stefanofinetti/MF_OverHead_Panel/STL Files/FaceDown_Printing/OVHD_PANEL_APU_UPPER_LAYER_TRASP.stl

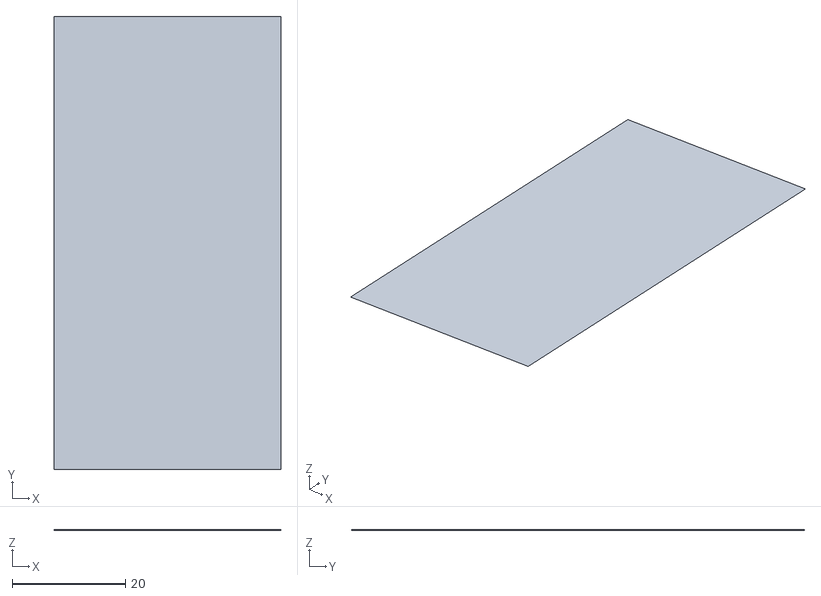
[picture p44: CAD file, 2025-06-21]
STL Files/FaceDown_Printing/OVHD_PANEL_APU_UPPER_LAYER_TRASP.stl
40.0 x 80.0 x 0.1
