stefanofinetti/MF_OverHead_Panel/STL Files/OVHD_OPEN_ON_KORRY_BUTTON_BLACK.stl

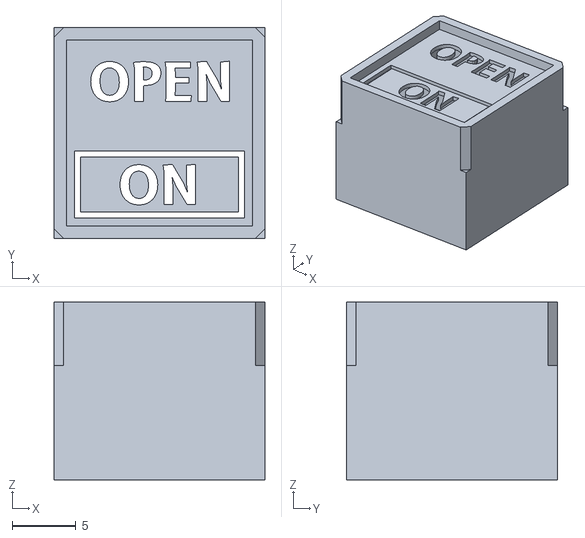
[picture p45: CAD file, 2025-01-15]
STL Files/OVHD_OPEN_ON_KORRY_BUTTON_BLACK.stl
16.6 x 16.6 x 14.0
