stefanofinetti/MF_OverHead_Panel/STL Files/FaceDown_Printing/OVHD_PANEL_APU_FRAME_TRASP.stl

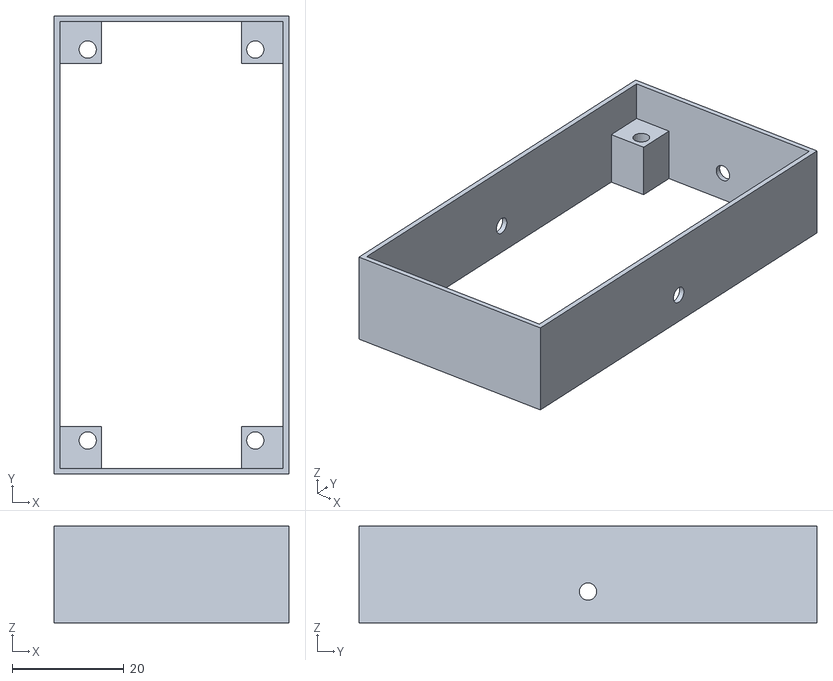
[picture p46: CAD file, 2025-06-21]
STL Files/FaceDown_Printing/OVHD_PANEL_APU_FRAME_TRASP.stl
42.0 x 82.0 x 17.3
