stefanofinetti/MF_OverHead_Panel/STL Files/Levers/obj_2_emer_lts.stl

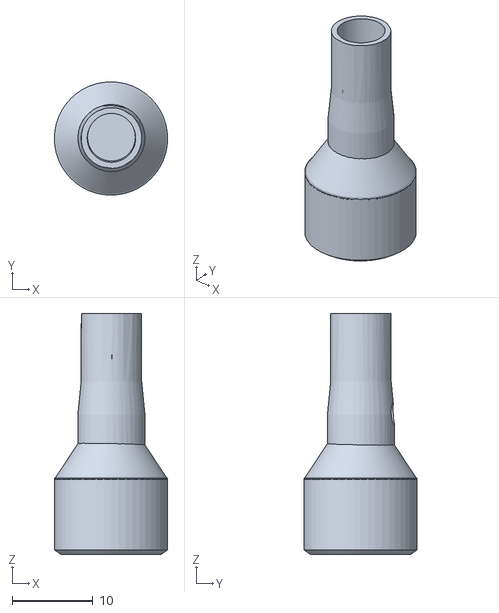
[picture p47: CAD file, 2026-09-29]
STL Files/Levers/obj_2_emer_lts.stl
14.0 x 14.0 x 29.8
