stefanofinetti/MF_OverHead_Panel/STL Files/Levers/Landing-Stem-Landing Lights Stem.stl

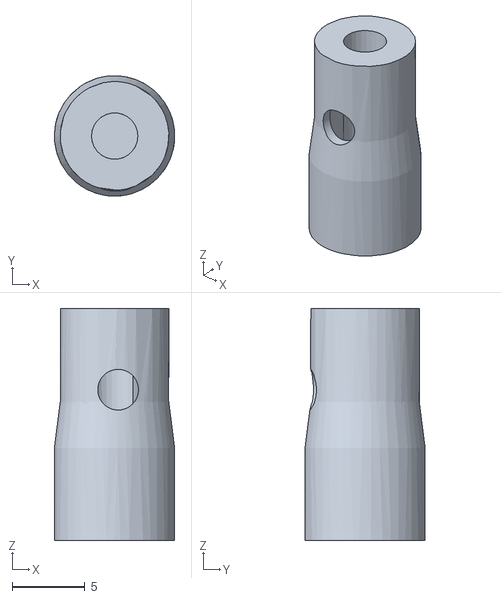
[picture p48: CAD file, 2026-09-29]
STL Files/Levers/Landing-Stem-Landing Lights Stem.stl
8.30 x 8.30 x 16.0
