stefanofinetti/MF_OverHead_Panel/STL Files/OVHD_FAULT_OFF_KORRY_BUTTON_TRANSP.stl

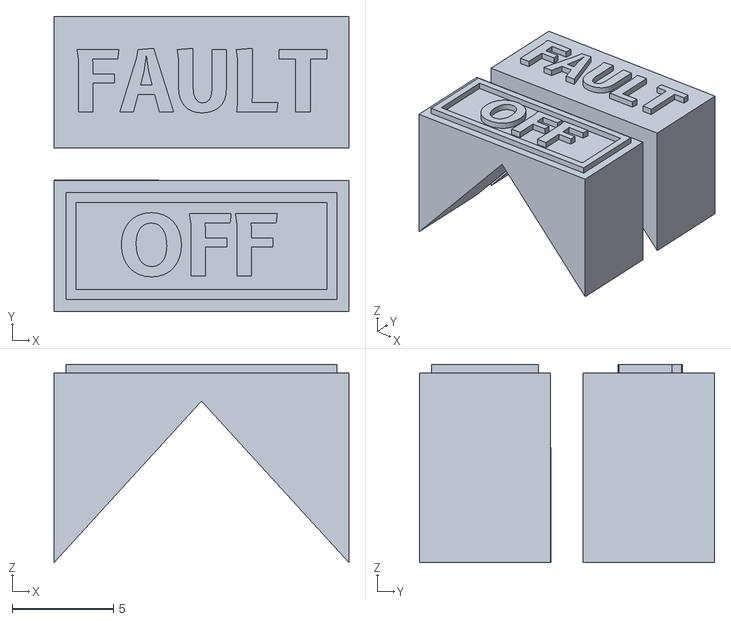
[picture p49: CAD file, 2025-01-15]
STL Files/OVHD_FAULT_OFF_KORRY_BUTTON_TRANSP.stl
14.6 x 14.6 x 9.82
