stefanofinetti/MF_OverHead_Panel/STL Files/Levers/landing-lights.stl

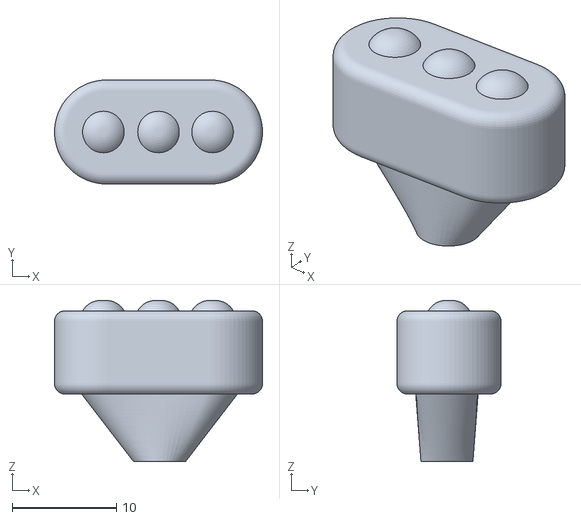
[picture p50: CAD file, 2025-01-14]
STL Files/Levers/landing-lights.stl
20.0 x 10.0 x 15.5
