stefanofinetti/MF_OverHead_Panel/STL Files/OVHD_KORRY_BUTTONS_SET.3mf

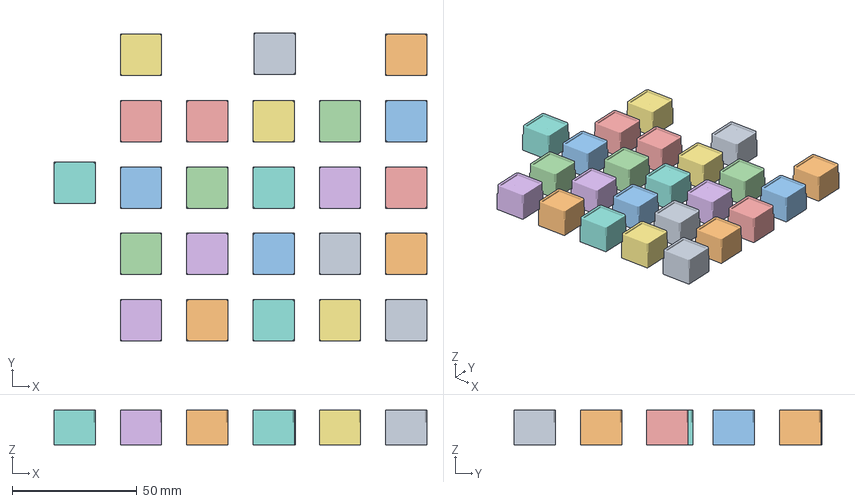
[picture p51: CAD file, 2025-01-15]
STL Files/OVHD_KORRY_BUTTONS_SET.3mf
149.6 x 123.5 x 14.0 mm
OVHD_AVAIL_ON_KORRY_BUTTON_BLACK x 2
OVHD_ON_KORRY_BUTTON_BLACK
OVHD_FAULT_ON_KORRY_BUTTON_BLACK x 5
OVHD_FAULT_OFF_KORRY_BUTTON_BLACK x 12
OVHD_OPEN_ON_KORRY_BUTTON_BLACK
OVHD_OFF_KORRY_BUTTON_BLACK x 3
