stefanofinetti/MF_OverHead_Panel/STL Files/OVHD_ON_KORRY_BUTTON_TRASP.stl

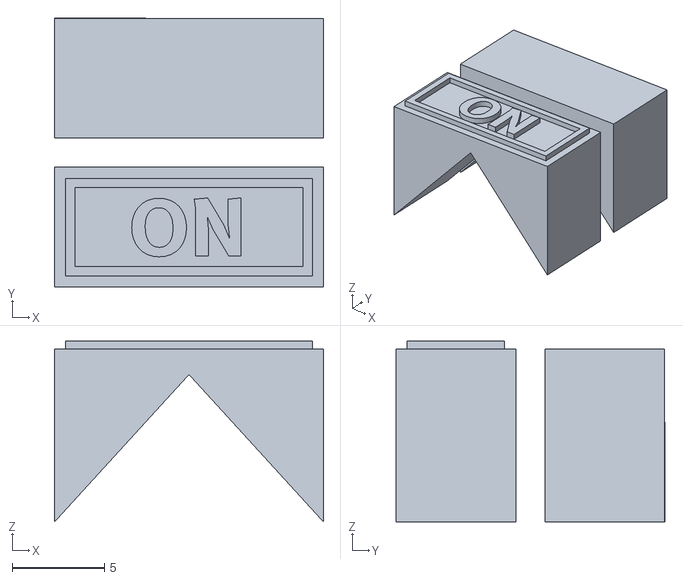
[picture p52: CAD file, 2025-01-15]
STL Files/OVHD_ON_KORRY_BUTTON_TRASP.stl
14.6 x 14.6 x 9.82
