stefanofinetti/MF_OverHead_Panel/STL Files/Levers/taxi-light.stl

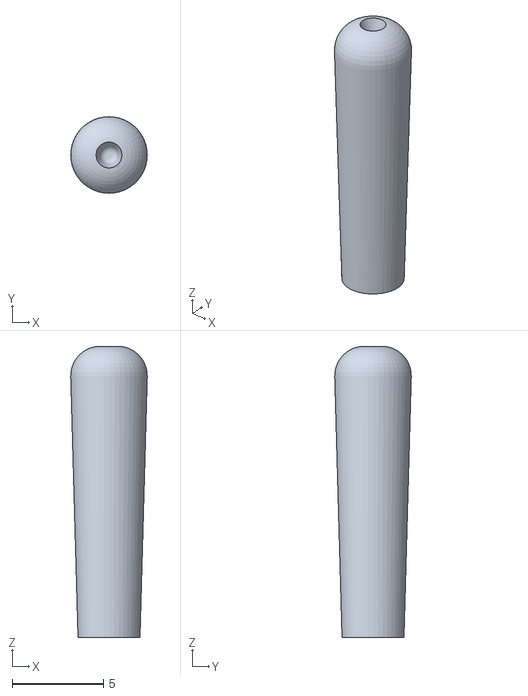
[picture p53: CAD file, 2025-01-14]
STL Files/Levers/taxi-light.stl
4.20 x 4.20 x 16.0
