stefanofinetti/MF_OverHead_Panel/STL Files/Levers/strobe-light.stl

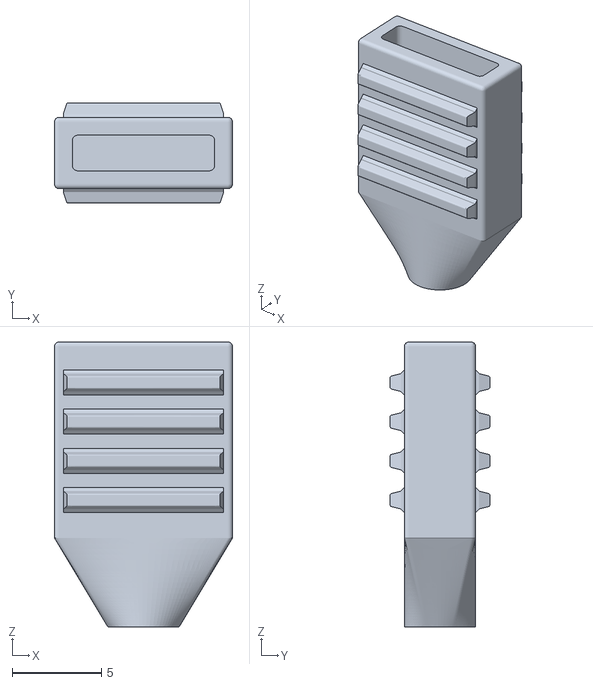
[picture p54: CAD file, 2025-01-14]
STL Files/Levers/strobe-light.stl
10.0 x 5.60 x 16.0
