stefanofinetti/MF_OverHead_Panel/STL Files/OVHD_PANEL_EXTLT.3mf

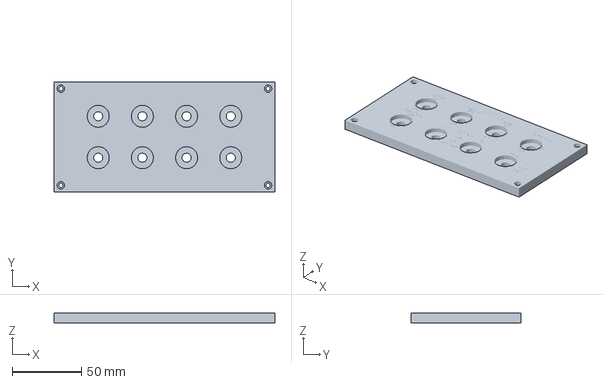
[picture p56: CAD file, 2025-01-14]
STL Files/OVHD_PANEL_EXTLT.3mf
160.0 x 80.0 x 7.56 mm
