stefanofinetti/MF_OverHead_Panel/STL Files/OVHD_PANEL_SIGNS_BLACK.stl

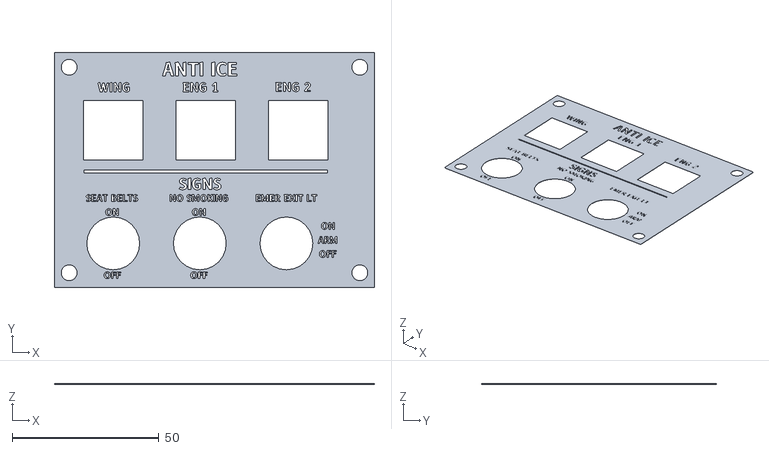
[picture p57: CAD file, 2025-01-14]
STL Files/OVHD_PANEL_SIGNS_BLACK.stl
109.0 x 80.0 x 0.42
