stefanofinetti/MF_OverHead_Panel/STL Files/OVHD_PANEL_SIGNS.3mf

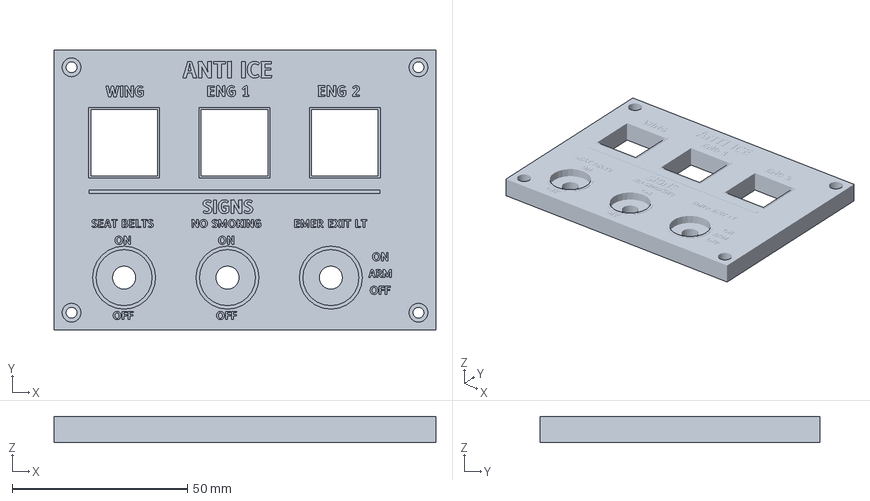
[picture p58: CAD file, 2025-01-14]
STL Files/OVHD_PANEL_SIGNS.3mf
109.0 x 80.0 x 7.56 mm
