stefanofinetti/MF_OverHead_Panel/STL Files/OVHD_PANEL_EXTLT_GRAY.stl

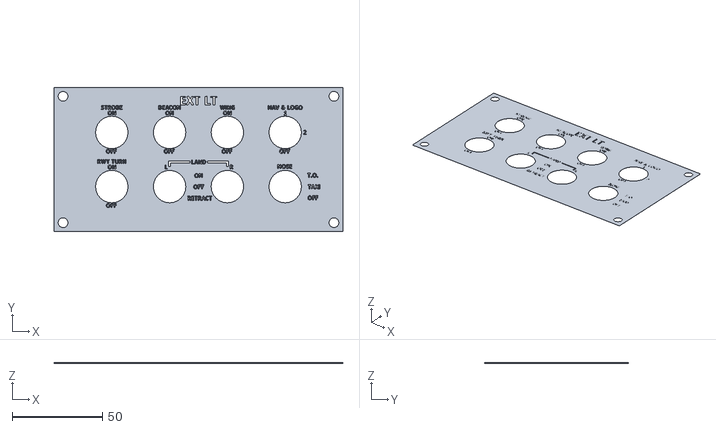
[picture p59: CAD file, 2025-01-14]
STL Files/OVHD_PANEL_EXTLT_GRAY.stl
160.0 x 80.0 x 0.42
