stefanofinetti/MF_OverHead_Panel/STL Files/OVHD_PANEL_SIGNS_TRASP.stl

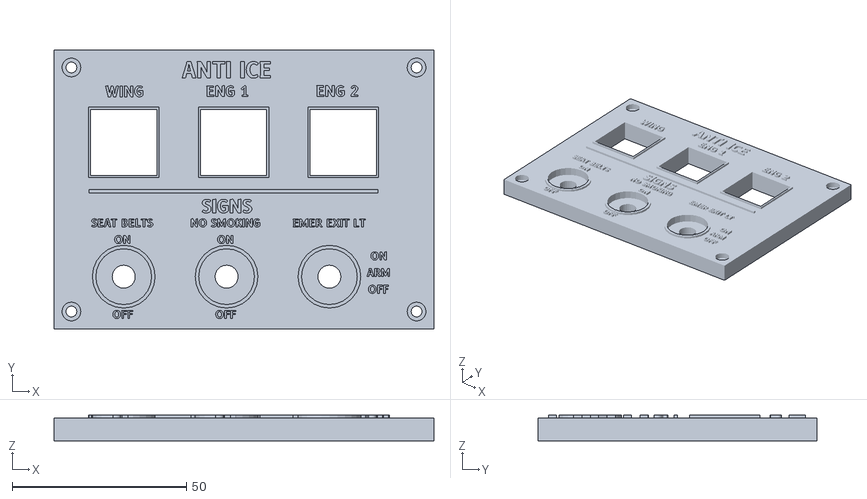
[picture p61: CAD file, 2025-01-14]
STL Files/OVHD_PANEL_SIGNS_TRASP.stl
109.0 x 80.0 x 7.42
