stefanofinetti/MF_OverHead_Panel/STL Files/OVHD_Switching_Knobs .3mf

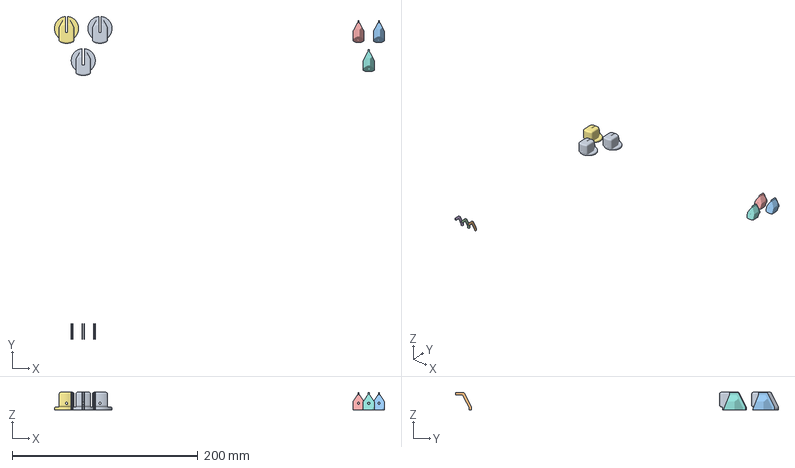
[picture p62: CAD file, 2025-01-14]
STL Files/OVHD_Switching_Knobs .3mf
355.2 x 347.6 x 19.0 mm
ecam-switching-knobs-ma22-knob-body.stl x 3
ecam-switching-knobs-ma22-black-line-surrounds.stl x 3
ecam-switching-knobs-ma22-light-pipe-body.stl x 3
