stefanofinetti/MF_OverHead_Panel/STL Files/OVHD_PANEL_EXTLT_TRASP.stl

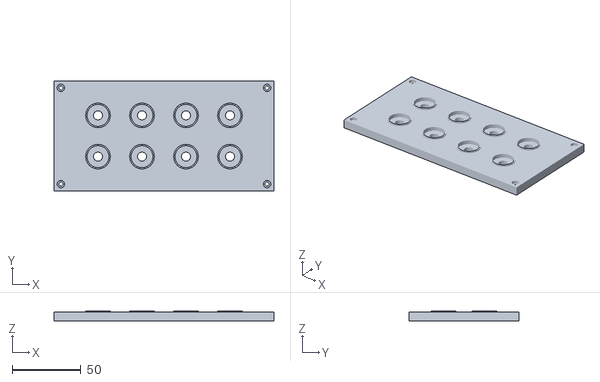
[picture p63: CAD file, 2025-01-14]
STL Files/OVHD_PANEL_EXTLT_TRASP.stl
160.0 x 80.0 x 7.42
