stefanofinetti/MF_OverHead_Panel/STL Files/OVHD_PANEL_LOWER_LEFT_CASE_BLACK.3mf

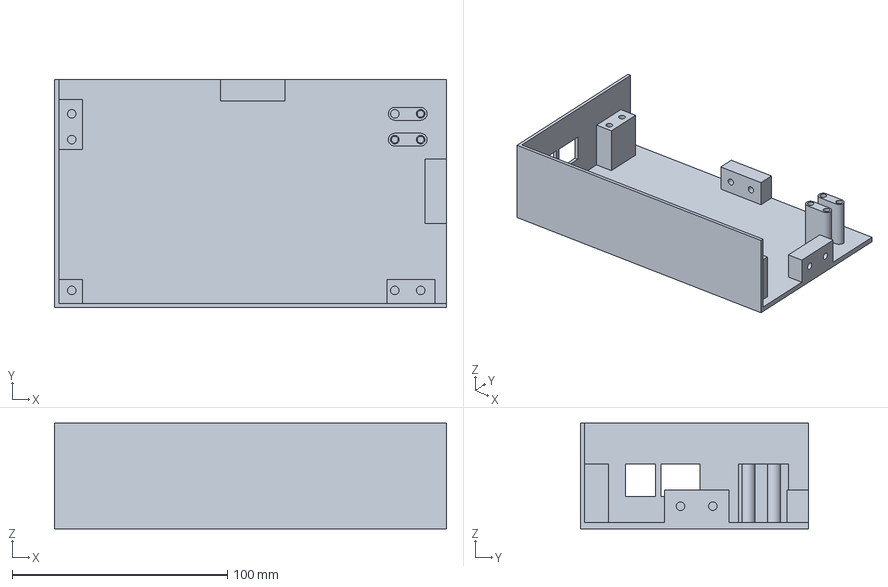
[picture p64: CAD file, 2025-01-14]
STL Files/OVHD_PANEL_LOWER_LEFT_CASE_BLACK.3mf
182.0 x 106.0 x 49.0 mm
