stefanofinetti/MF_OverHead_Panel/STL Files/OVHD_PANEL_UPPER_RIGHT_CASE_BLACK.3mf

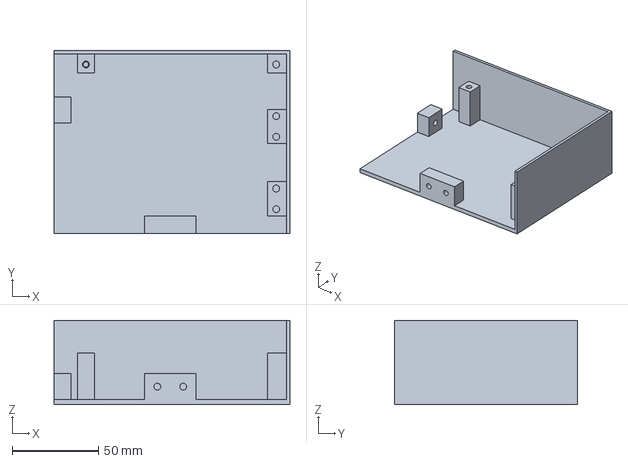
[picture p65: CAD file, 2025-01-14]
STL Files/OVHD_PANEL_UPPER_RIGHT_CASE_BLACK.3mf
137.0 x 106.0 x 49.0 mm
