stefanofinetti/MF_OverHead_Panel/STL Files/OVHD_PANEL_SIGNS_WHITE.stl

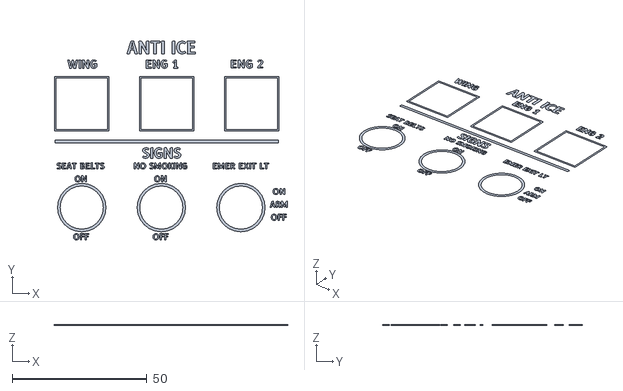
[picture p66: CAD file, 2025-01-14]
STL Files/OVHD_PANEL_SIGNS_WHITE.stl
86.4 x 73.8 x 0.14
