stefanofinetti/MF_OverHead_Panel/STL Files/OVHD_KORRY_CASE_SHORT_TRIPLE_19x19.stl

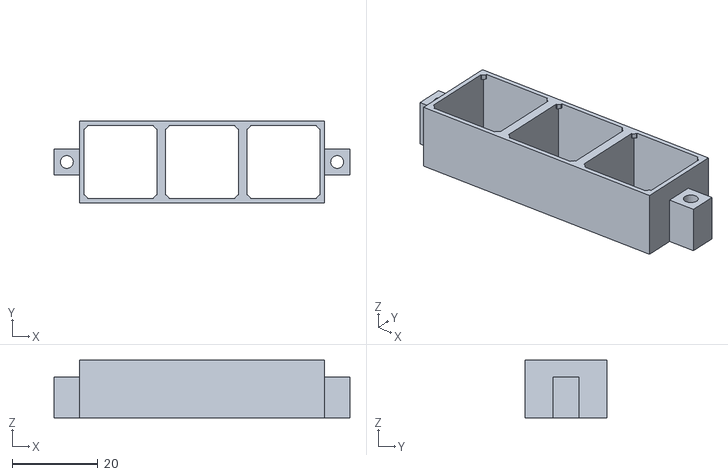
[picture p67: CAD file, 2024-12-02]
STL Files/OVHD_KORRY_CASE_SHORT_TRIPLE_19x19.stl
69.0 x 19.0 x 13.5
