stefanofinetti/MF_OverHead_Panel/STL Files/OVHD_PANEL_FUEL_TRASP.stl

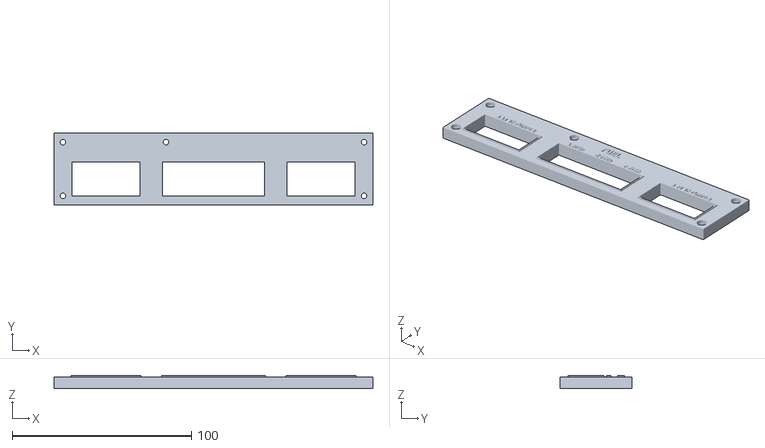
[picture p68: CAD file, 2024-12-02]
STL Files/OVHD_PANEL_FUEL_TRASP.stl
178.0 x 40.0 x 7.42
