stefanofinetti/MF_OverHead_Panel/STL Files/OVHD_PANEL_FUEL_GRAY.stl

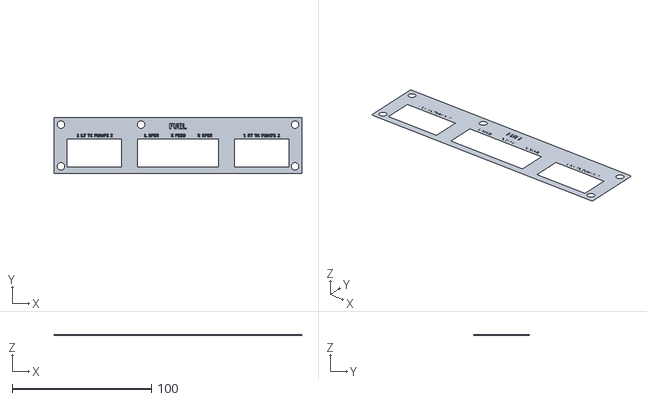
[picture p69: CAD file, 2024-12-02]
STL Files/OVHD_PANEL_FUEL_GRAY.stl
178.0 x 40.0 x 0.42
