stefanofinetti/MF_OverHead_Panel/STL Files/OVHD_PANEL_FUEL_WHITE.stl

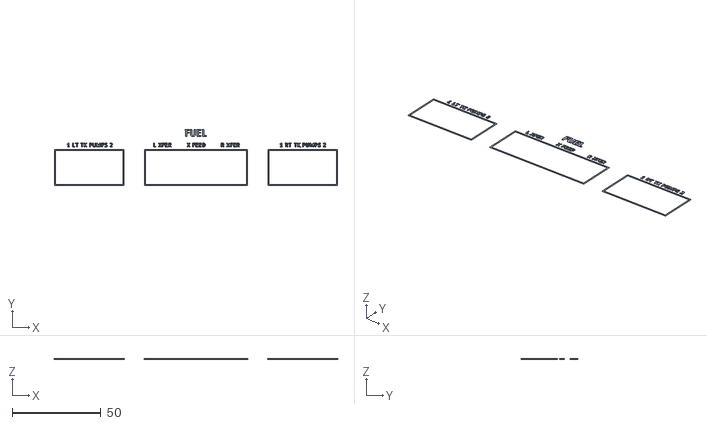
[picture p72: CAD file, 2024-12-02]
STL Files/OVHD_PANEL_FUEL_WHITE.stl
159.2 x 31.6 x 0.14
