stefanofinetti/MF_OverHead_Panel/STL Files/OVHD_PANEL_AIR-COND_FRAME_WHITE.stl

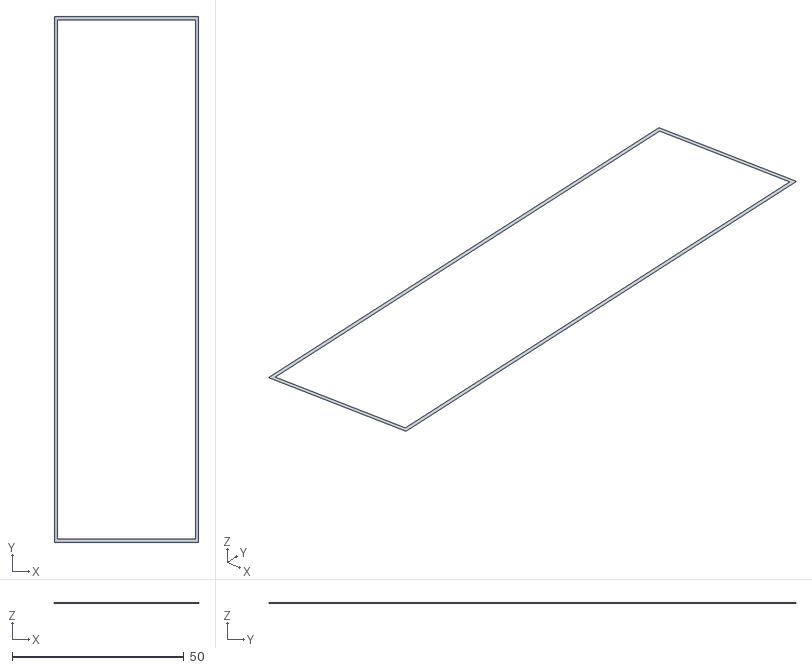
[picture p73: CAD file, 2024-12-02]
STL Files/OVHD_PANEL_AIR-COND_FRAME_WHITE.stl
42.0 x 153.0 x 0.14
