stefanofinetti/MF_OverHead_Panel/STL Files/OVHD_PANEL_AIRCOND_GRAY.stl

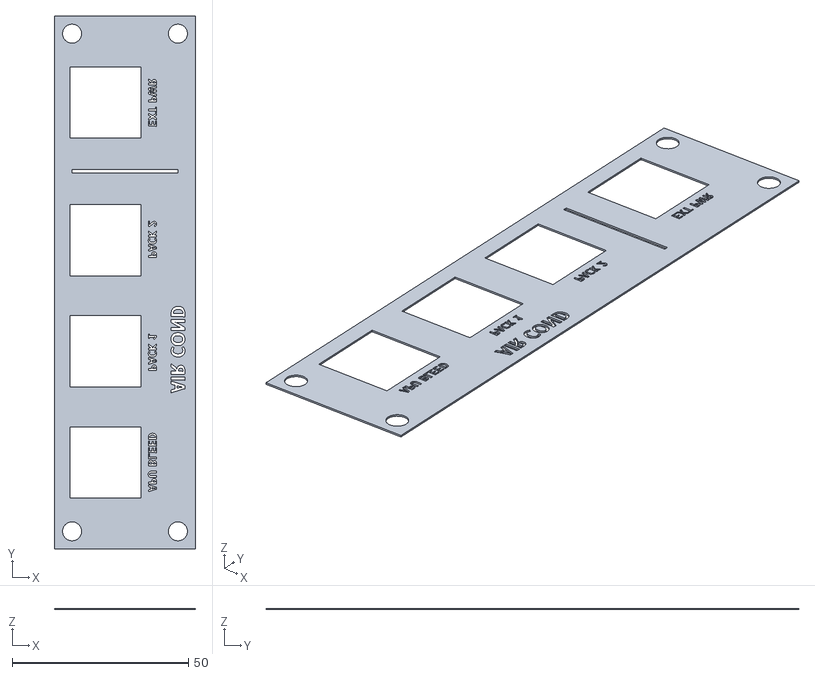
[picture p74: CAD file, 2024-12-02]
STL Files/OVHD_PANEL_AIRCOND_GRAY.stl
40.0 x 151.0 x 0.42
