stefanofinetti/MF_OverHead_Panel/STL Files/OVHD_PANEL_ELEC_FRAME_TRASP.stl

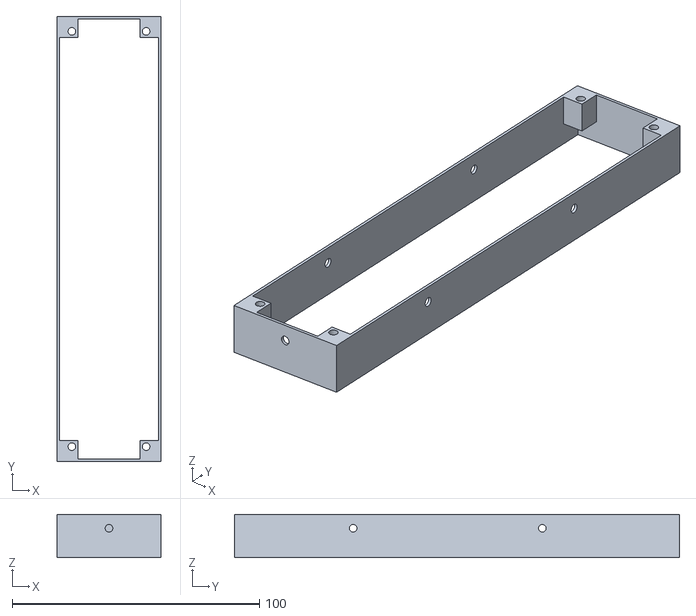
[picture p75: CAD file, 2024-12-02]
STL Files/OVHD_PANEL_ELEC_FRAME_TRASP.stl
42.0 x 180.0 x 17.4
