stefanofinetti/MF_OverHead_Panel/STL Files/OVHD_PANEL_GPWS_GRAY.stl

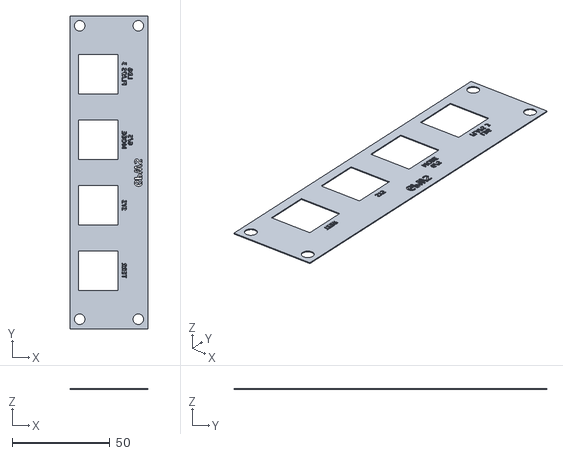
[picture p76: CAD file, 2024-12-02]
STL Files/OVHD_PANEL_GPWS_GRAY.stl
40.0 x 160.0 x 0.42
