stefanofinetti/MF_OverHead_Panel/STL Files/OVHD_PANEL_AIRCOND_WHITE.stl

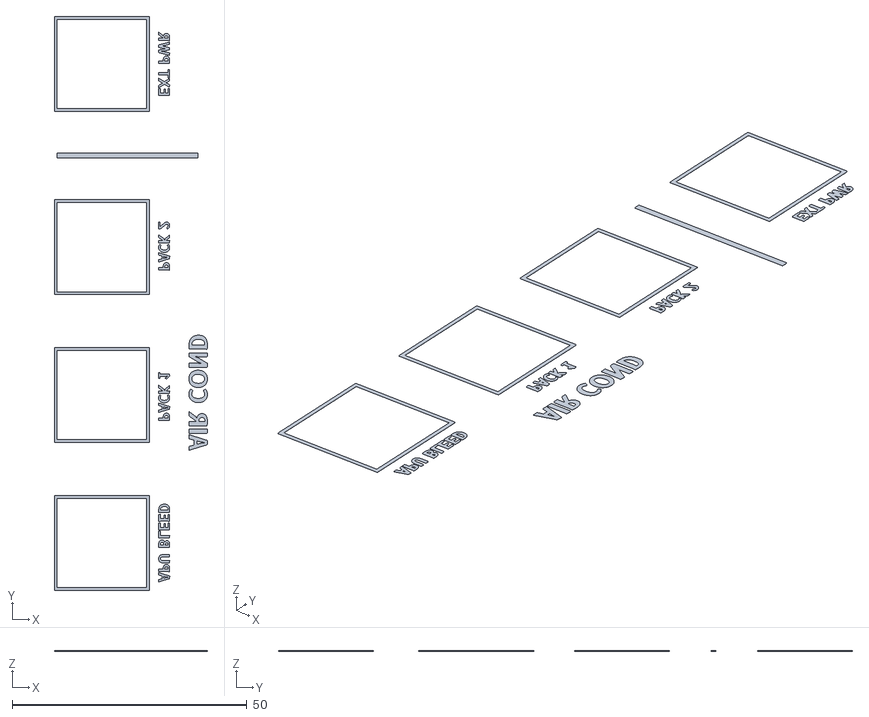
[picture p77: CAD file, 2024-12-02]
STL Files/OVHD_PANEL_AIRCOND_WHITE.stl
32.6 x 122.2 x 0.14
