stefanofinetti/MF_OverHead_Panel/STL Files/OVHD_PANEL_APU_CONCEPT_BLACK.stl

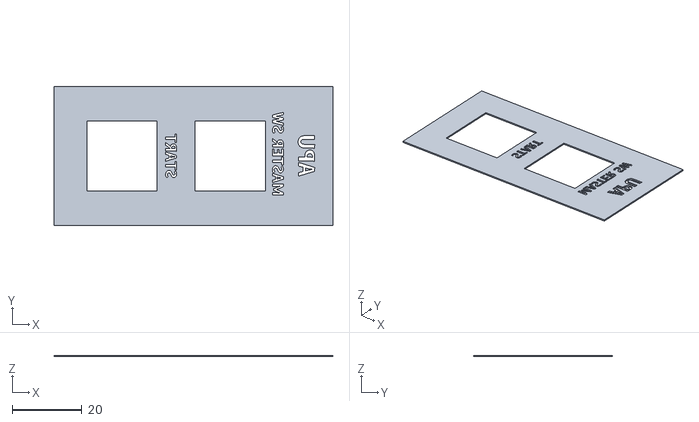
[picture p78: CAD file, 2024-12-02]
STL Files/OVHD_PANEL_APU_CONCEPT_BLACK.stl
80.0 x 40.0 x 0.42
