stefanofinetti/MF_OverHead_Panel/STL Files/OVHD_PANEL_ELEC_GRAY.stl

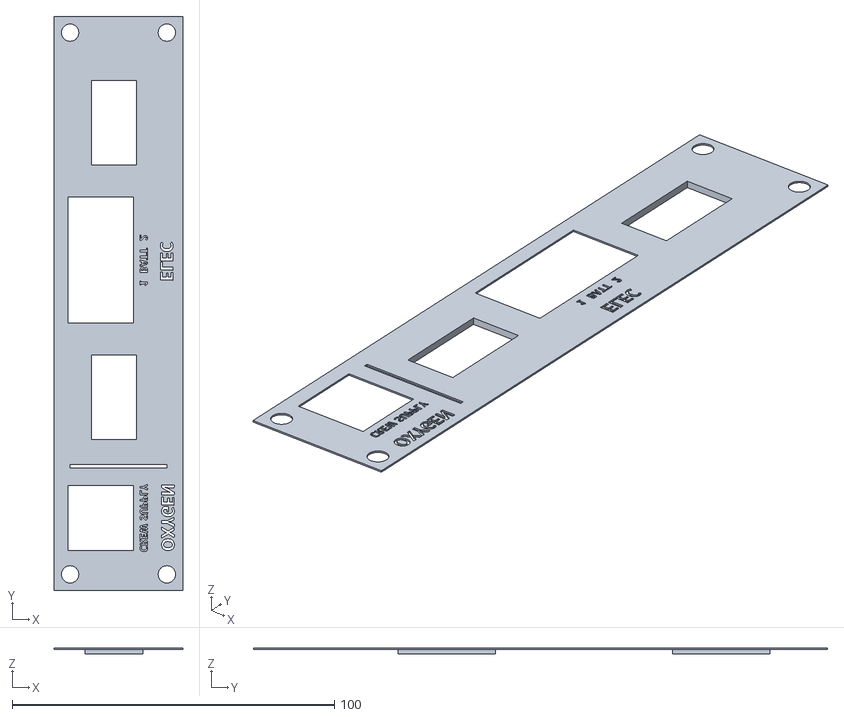
[picture p79: CAD file, 2024-12-02]
STL Files/OVHD_PANEL_ELEC_GRAY.stl
40.0 x 178.0 x 1.82
