stefanofinetti/MF_OverHead_Panel/STL Files/OVHD_KORRY_CASE_SHORT_19x19.stl

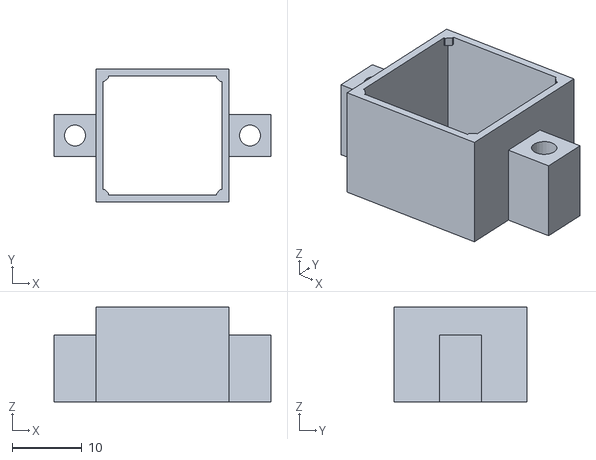
[picture p81: CAD file, 2024-12-02]
STL Files/OVHD_KORRY_CASE_SHORT_19x19.stl
31.0 x 19.0 x 13.5
