stefanofinetti/MF_OverHead_Panel/STL Files/OVHD_PANEL_ELEC_WHITE.stl

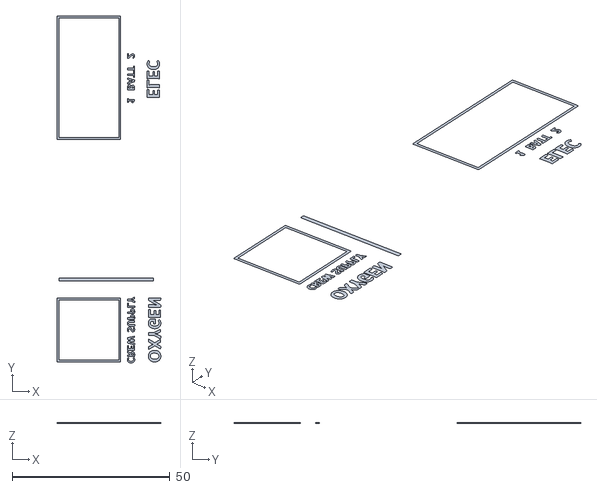
[picture p82: CAD file, 2024-12-02]
STL Files/OVHD_PANEL_ELEC_WHITE.stl
33.0 x 110.1 x 0.14
