stefanofinetti/MF_OverHead_Panel/STL Files/OVHD_PANEL_ELEC_FRAME_WHITE.stl

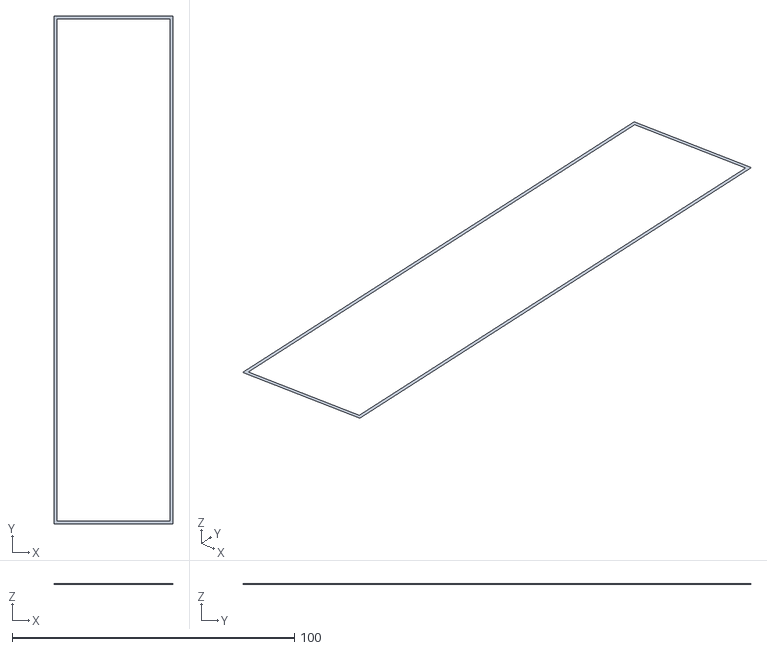
[picture p83: CAD file, 2024-12-02]
STL Files/OVHD_PANEL_ELEC_FRAME_WHITE.stl
42.0 x 180.0 x 0.14
