stefanofinetti/MF_OverHead_Panel/STL Files/OVHD_PANEL_APU_FRAME_TRASP.stl

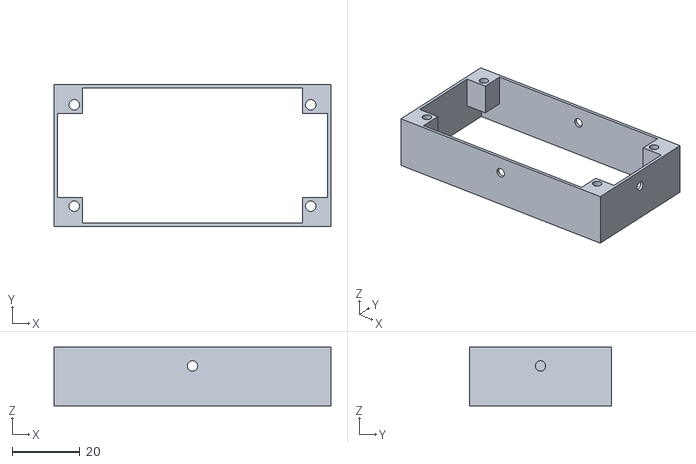
[picture p84: CAD file, 2024-12-02]
STL Files/OVHD_PANEL_APU_FRAME_TRASP.stl
82.0 x 42.0 x 17.4
