stefanofinetti/MF_OverHead_Panel/STL Files/OVHD_PANEL_EXTLT_WHITE.stl

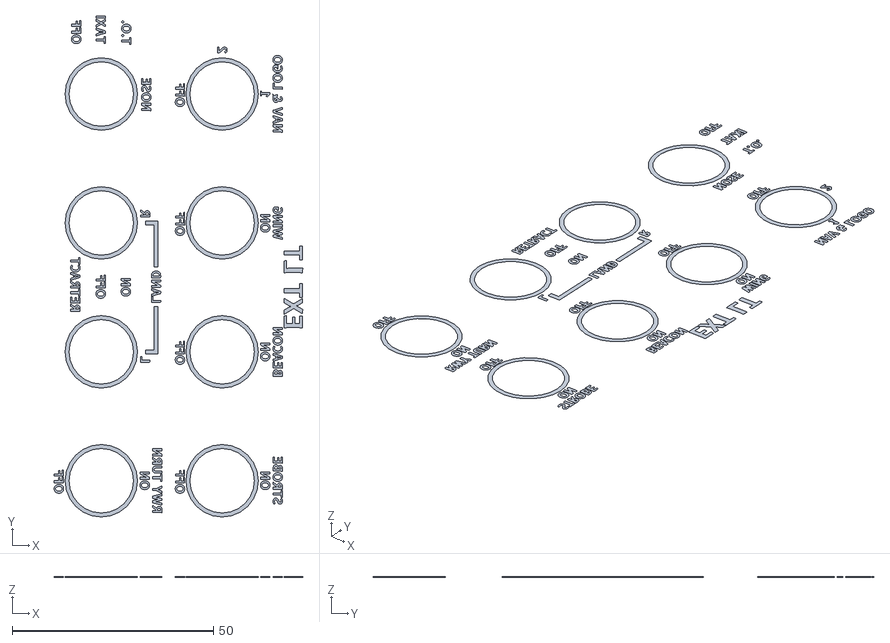
[picture p85: CAD file, 2024-12-02]
STL Files/OVHD_PANEL_EXTLT_WHITE.stl
61.7 x 124.4 x 0.14
