stefanofinetti/MF_OverHead_Panel/STL Files/OVHD_PANEL_GPWS_WHITE.stl

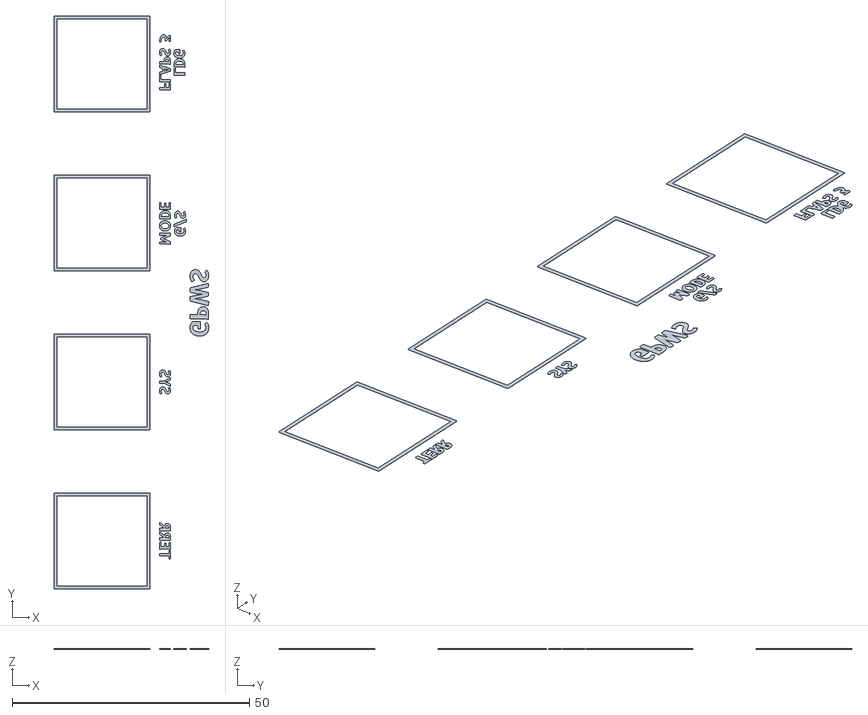
[picture p86: CAD file, 2024-12-02]
STL Files/OVHD_PANEL_GPWS_WHITE.stl
32.6 x 120.7 x 0.14
