stefanofinetti/MF_OverHead_Panel/STL Files/OVHD_FAULT_OFF_KORRY_BUTTON.3mf

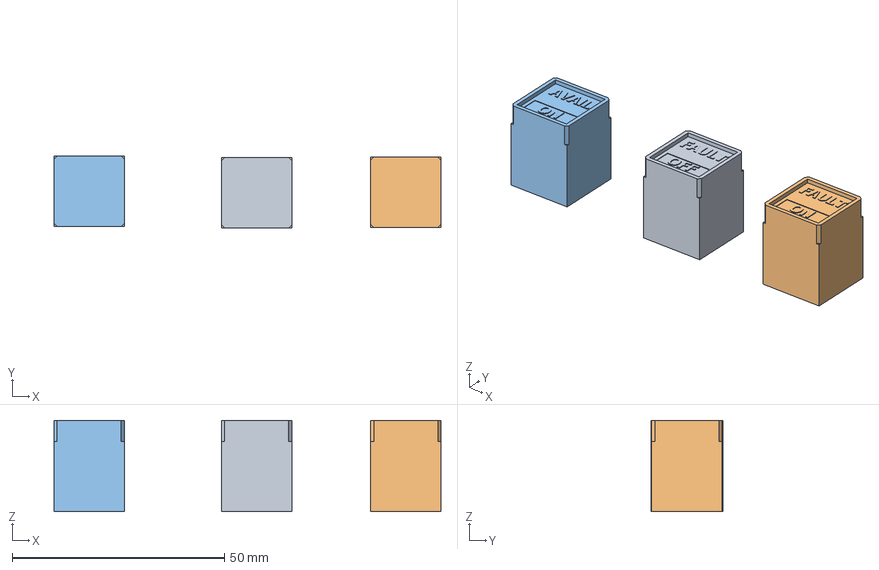
[picture p87: CAD file, 2024-12-02]
STL Files/OVHD_FAULT_OFF_KORRY_BUTTON.3mf
91.3 x 17.0 x 21.5 mm
OVHD_FAULT_OFF_KORRY_BUTTON_BLACK
OVHD_FAULT_ON_KORRY_BUTTON_BLACK
OVHD_AVAIL_ON_KORRY_BUTTON_BLACK
