stefanofinetti/MF_OverHead_Panel/STL Files/OVHD_PANEL_FUEL.3mf

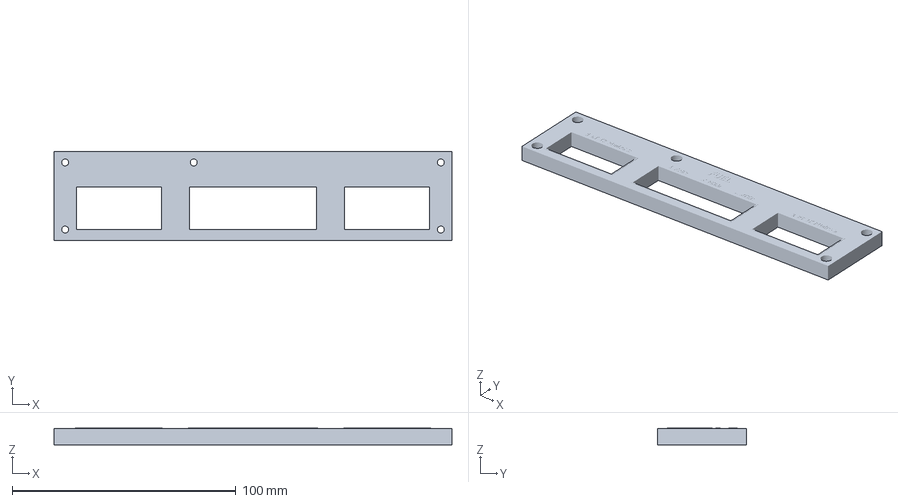
[picture p88: CAD file, 2024-12-02]
STL Files/OVHD_PANEL_FUEL.3mf
178.0 x 40.0 x 7.56 mm
