stefanofinetti/MF_OverHead_Panel/STL Files/OVHD_KORRY_CASE_SET_19x19.3mf

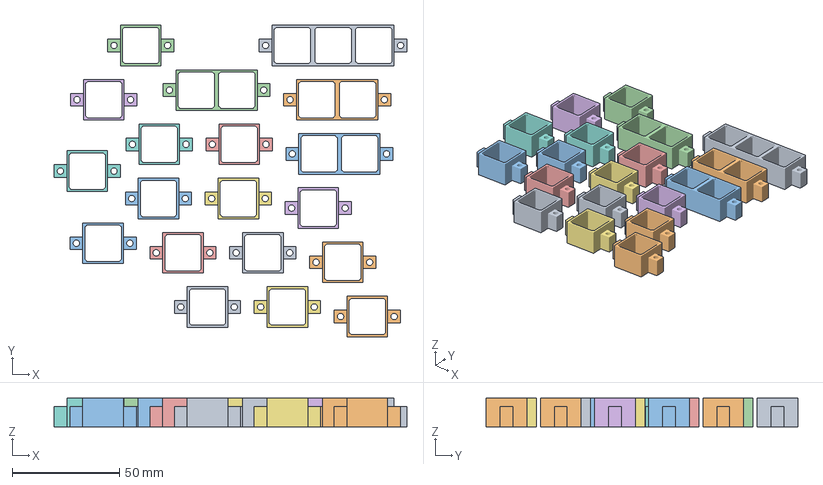
[picture p90: CAD file, 2024-12-02]
STL Files/OVHD_KORRY_CASE_SET_19x19.3mf
164.7 x 145.5 x 13.5 mm
OVHD_KORRY_CASE_SHORT_TRIPLE_19x19.stl
OVHD_KORRY_CASE_SHORT_DUAL_19x19.stl x 3
OVHD_KORRY_CASE_SHORT_19x19.stl x 15
