stefanofinetti/MF_OverHead_Panel/STL Files/OVHD_PANEL_APU_CONCEPT.3mf

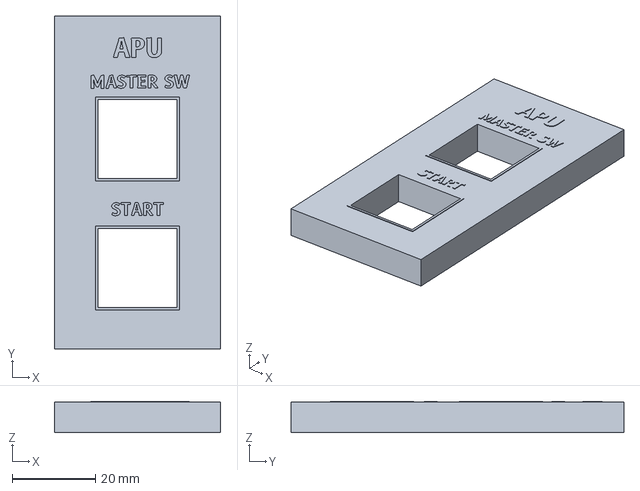
[picture p91: CAD file, 2024-12-02]
STL Files/OVHD_PANEL_APU_CONCEPT.3mf
40.0 x 80.0 x 7.56 mm
