stefanofinetti/MF_OverHead_Panel/STL Files/OVHD_PANEL_GPWS_TRASP.stl

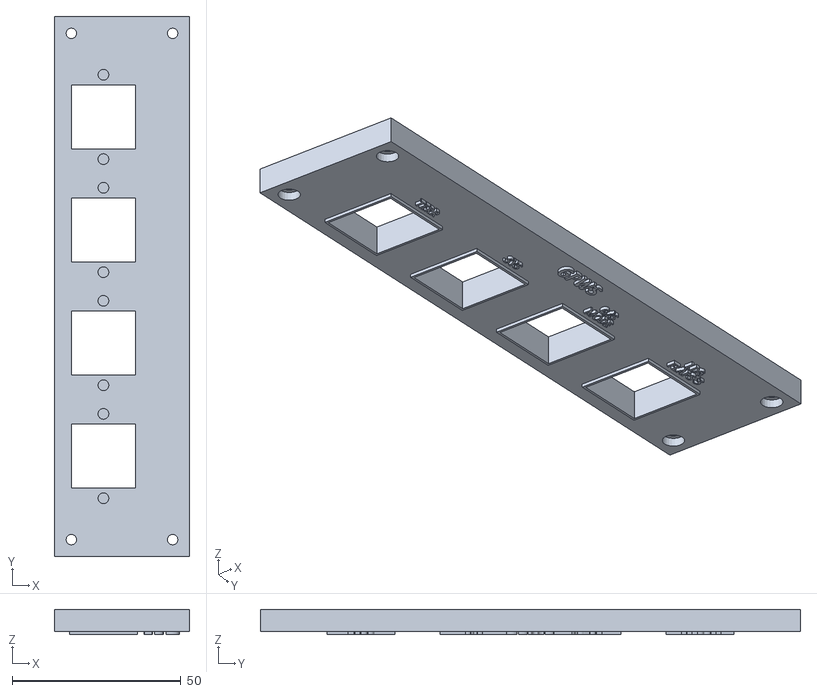
[picture p93: CAD file, 2024-12-02]
STL Files/OVHD_PANEL_GPWS_TRASP.stl
40.0 x 160.0 x 7.42
