stefanofinetti/MF_OverHead_Panel/STL Files/OVHD_PANEL_APU.3mf

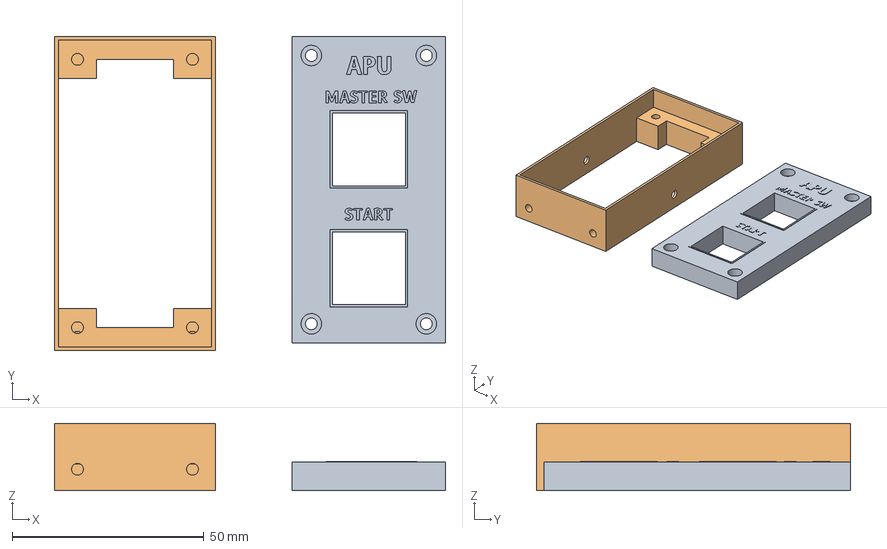
[picture p94: CAD file, 2024-12-02]
STL Files/OVHD_PANEL_APU.3mf
102.0 x 82.0 x 17.6 mm
OVHD_PANEL_APU_BLACK
OVHD_PANEL_APU_FRAME_TRASP
