stefanofinetti/MF_OverHead_Panel/STL Files/OVHD_PANEL_FRAME_03.3mf

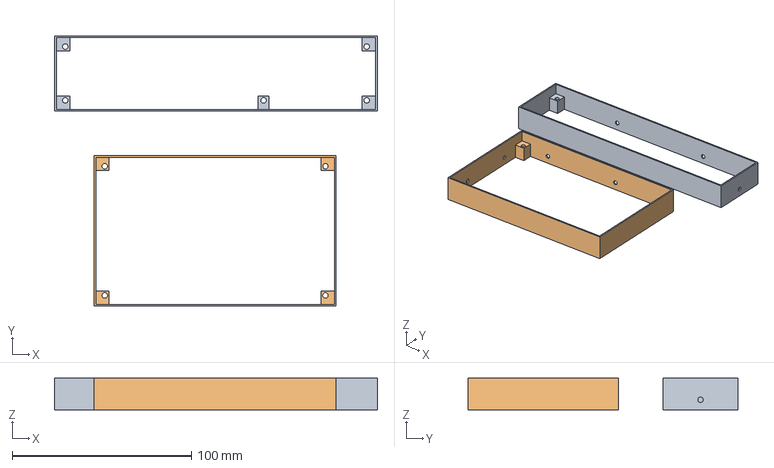
[picture p95: CAD file, 2024-12-02]
STL Files/OVHD_PANEL_FRAME_03.3mf
180.0 x 150.7 x 17.6 mm
OVHD_PANEL_FUEL_FRAME_TRASP
OVHD_PANEL_ADIRS_FRAME_TRASP
