stefanofinetti/MF_OverHead_Panel/STL Files/OVHD_PANEL_EXT-LT_FRAME_TRASP.stl

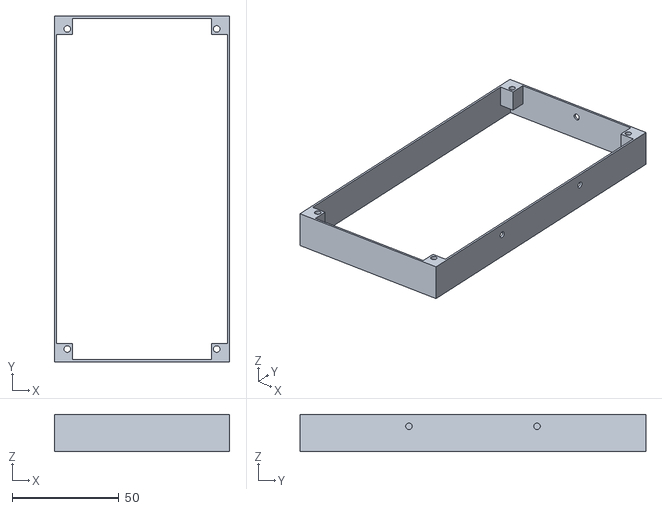
[picture p96: CAD file, 2024-12-02]
STL Files/OVHD_PANEL_EXT-LT_FRAME_TRASP.stl
82.0 x 162.0 x 17.4
