stefanofinetti/MF_OverHead_Panel/STL Files/OVHD_PANEL_ADIRS_WHITE.stl

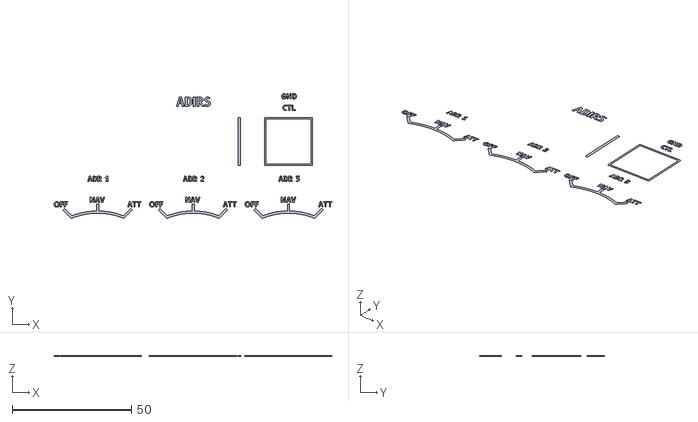
[picture p97: CAD file, 2024-12-02]
STL Files/OVHD_PANEL_ADIRS_WHITE.stl
116.5 x 52.4 x 0.14
