stefanofinetti/MF_OverHead_Panel/STL Files/OVHD_PANEL_FRAME_01.3mf

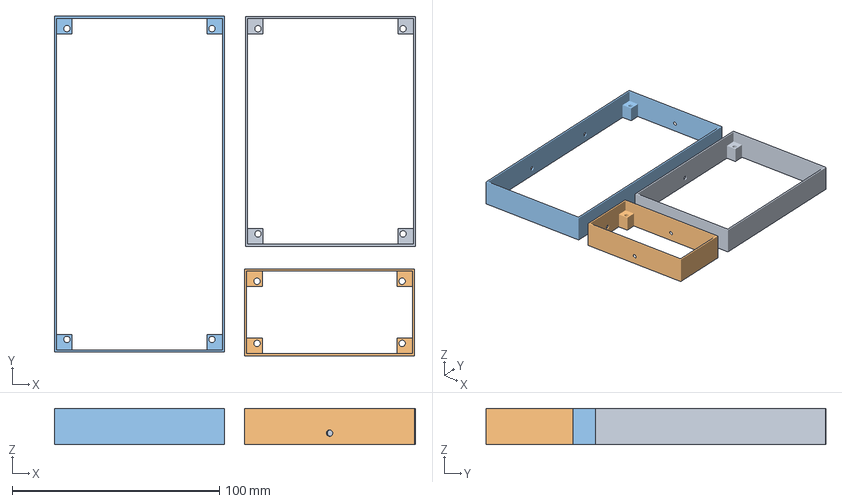
[picture p99: CAD file, 2024-12-02]
STL Files/OVHD_PANEL_FRAME_01.3mf
174.2 x 163.9 x 17.6 mm
OVHD_PANEL_ANTI-ICE-FRAME-TRASP
OVHD_PANEL_APU_FRAME_TRASP
OVHD_PANEL_EXT-LT_FRAME_TRASP
