stefanofinetti/MF_OverHead_Panel/STL Files/OVHD_PANEL_AIRCOND_TRASP.stl

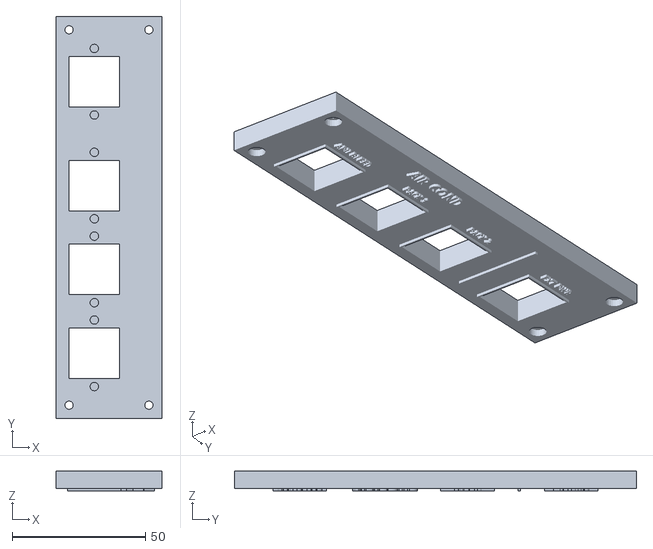
[picture p101: CAD file, 2024-12-02]
STL Files/OVHD_PANEL_AIRCOND_TRASP.stl
40.0 x 151.0 x 7.42
