stefanofinetti/MF_OverHead_Panel/STL Files/OVHD_PANEL_ANTI-ICE-FRAME-WHITE.stl

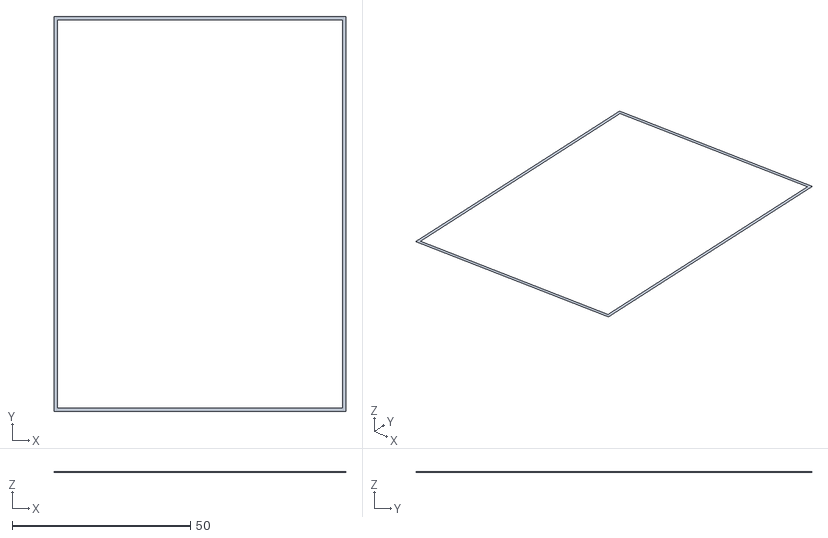
[picture p102: CAD file, 2024-12-02]
STL Files/OVHD_PANEL_ANTI-ICE-FRAME-WHITE.stl
82.0 x 111.0 x 0.14
