stefanofinetti/MF_OverHead_Panel/STL Files/OVHD_PANEL_APU_TRASP.stl

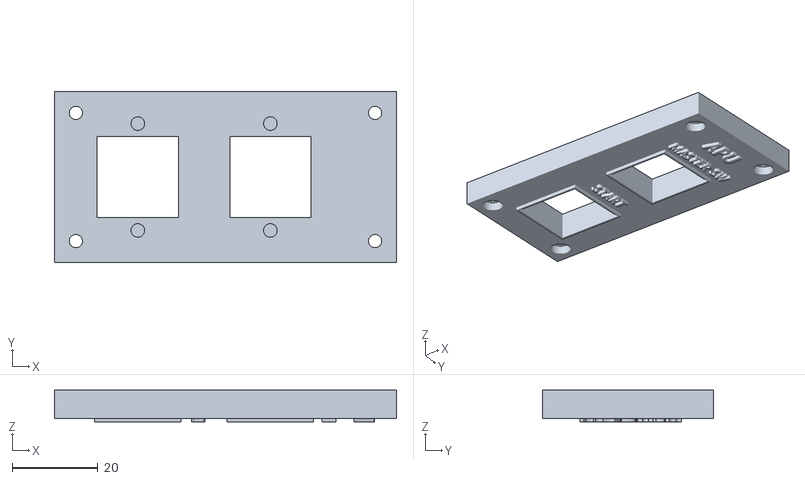
[picture p103: CAD file, 2024-12-02]
STL Files/OVHD_PANEL_APU_TRASP.stl
80.0 x 40.0 x 7.42
