stefanofinetti/MF_OverHead_Panel/STL Files/OVHD_PANEL_EXT-LT_FRAME_WHITE.stl

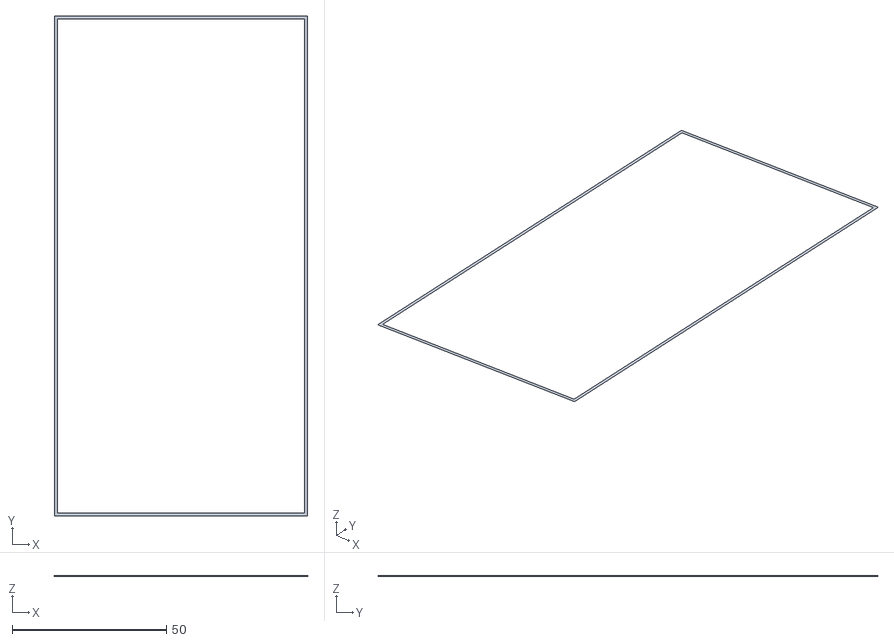
[picture p104: CAD file, 2024-12-02]
STL Files/OVHD_PANEL_EXT-LT_FRAME_WHITE.stl
82.0 x 162.0 x 0.14
