stefanofinetti/MF_OverHead_Panel/STL Files/OVHD_PANEL_GPWS.3mf

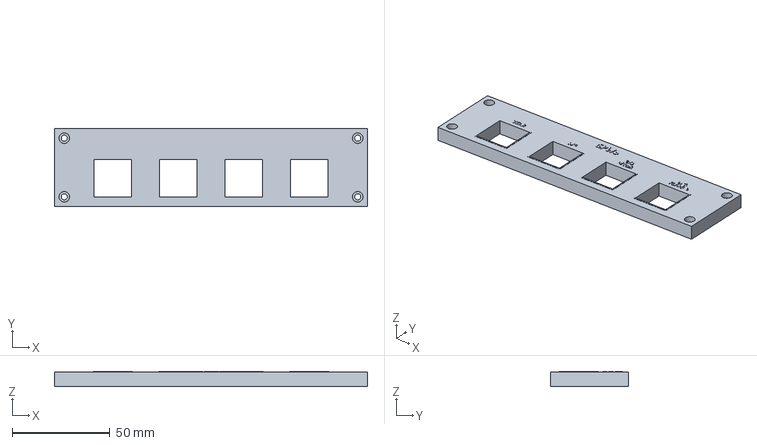
[picture p105: CAD file, 2024-12-02]
STL Files/OVHD_PANEL_GPWS.3mf
160.0 x 40.0 x 7.56 mm
