stefanofinetti/MF_OverHead_Panel/STL Files/OVHD_PANEL_ADIRS_FRAME_WHITE.stl

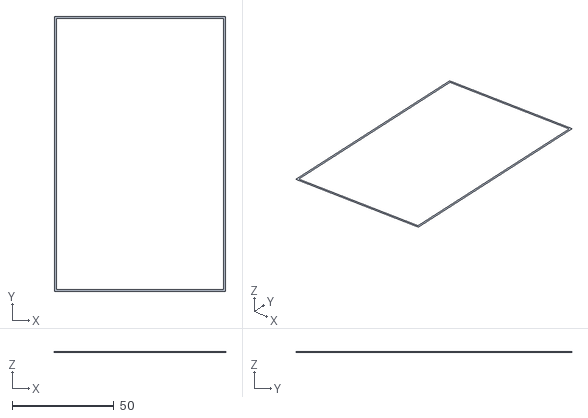
[picture p106: CAD file, 2024-12-02]
STL Files/OVHD_PANEL_ADIRS_FRAME_WHITE.stl
84.0 x 135.0 x 0.14
