stefanofinetti/MF_OverHead_Panel/STL Files/OVHD_PANEL_ANTI-ICE-FRAME-TRASP.stl

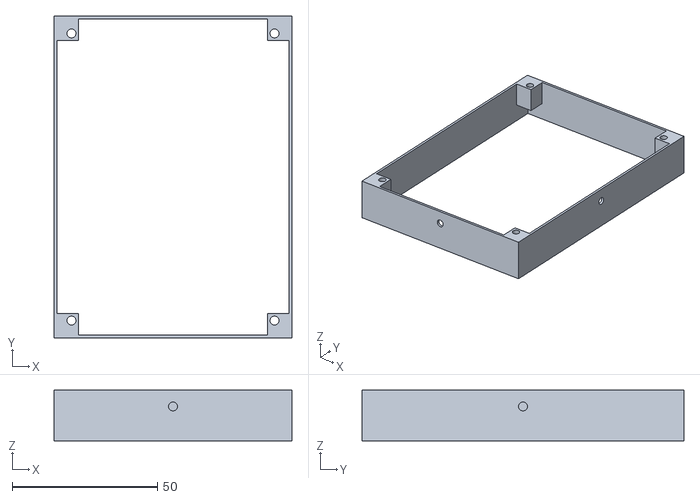
[picture p107: CAD file, 2024-12-02]
STL Files/OVHD_PANEL_ANTI-ICE-FRAME-TRASP.stl
82.0 x 111.0 x 17.4
