stefanofinetti/MF_OverHead_Panel/STL Files/OVHD_PANEL_ELEC.3mf

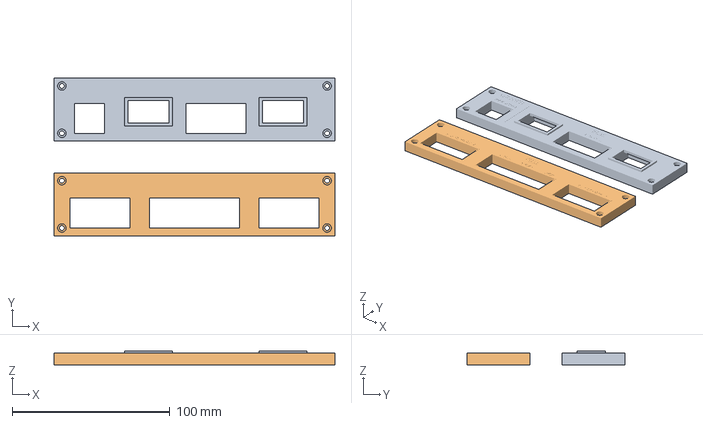
[picture p108: CAD file, 2024-12-02]
STL Files/OVHD_PANEL_ELEC.3mf
178.0 x 100.0 x 8.82 mm
OVHD_PANEL_ELEC_BLACK
OVHD_PANEL_FUEL_BLACK
