stefanofinetti/MF_OverHead_Panel/STL Files/OVHD_PANEL_FRAME_02.3mf

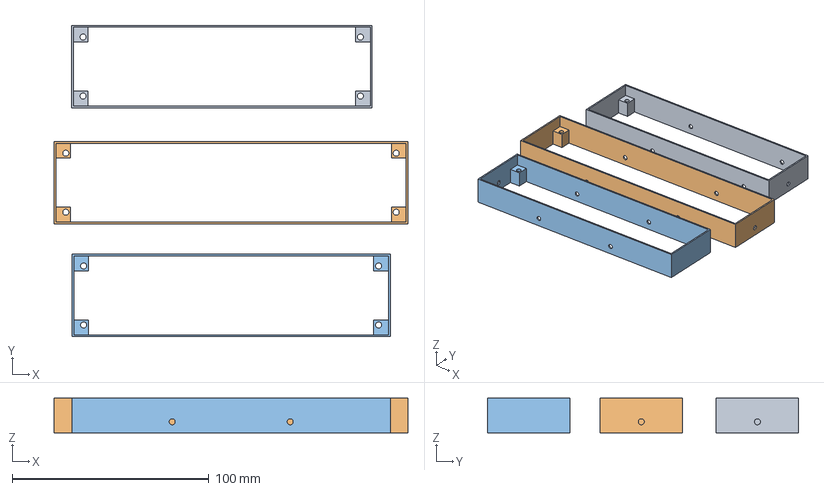
[picture p109: CAD file, 2024-12-02]
STL Files/OVHD_PANEL_FRAME_02.3mf
180.0 x 158.4 x 17.6 mm
OVHD_PANEL_AIR-COND_FRAME_TRASP
OVHD_PANEL_ELEC_FRAME_TRASP
OVHD_PANEL_GPWS_FRAME_TRASP
