stefanofinetti/MF_OverHead_Panel/STL Files/OVHD_PANEL_ELEC_BLACK.stl

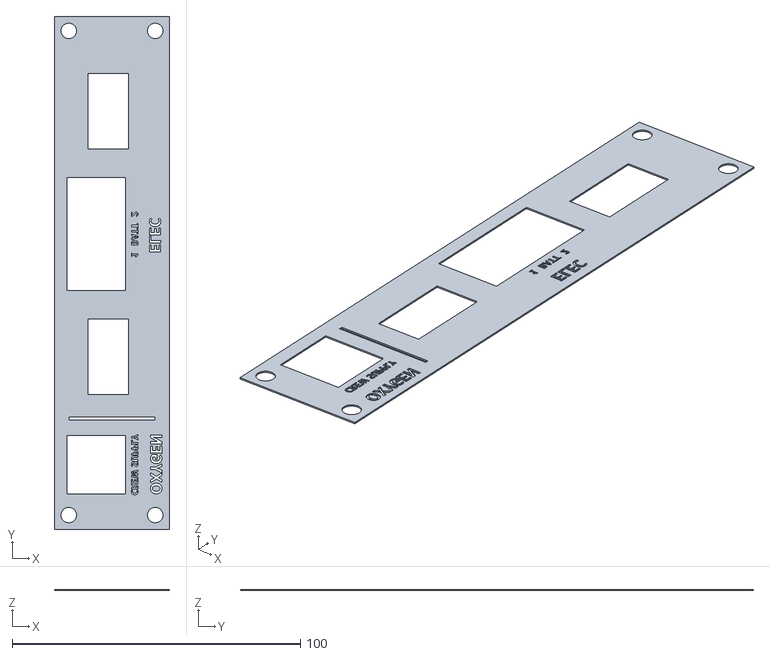
[picture p110: CAD file, 2024-12-02]
STL Files/OVHD_PANEL_ELEC_BLACK.stl
40.0 x 178.0 x 0.42
